jucgarciagon/ELECTROMYOGRAPHIC-SIGNALS/imagen/fortan1.png

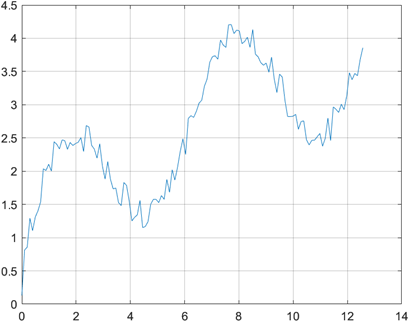
imagen/fortan1.png
