jucgarciagon/ELECTROMYOGRAPHIC-SIGNALS/proyectoV2.1.X/interrupts.c

/******************************************************************************/
/*Files to Include                                                            */
/******************************************************************************/

#if defined(__XC)
    #include <xc.h>         /* XC8 General Include File */
#elif defined(HI_TECH_C)
    #include <htc.h>        /* HiTech General Include File */
#elif defined(__18CXX)
    #include <p18cxxx.h>    /* C18 General Include File */
#endif

#if defined(__XC) || defined(HI_TECH_C)

#include <stdint.h>         /* For uint8_t definition */
#include <stdbool.h>        /* For true/false definition */

#endif

/******************************************************************************/
/* Interrupt Routines                                                         */
/******************************************************************************/

bool conversionADC;
bool entrada=0;

/* High-priority service */

#if defined(__XC) || defined(HI_TECH_C)
void interrupt high_isr(void)
#elif defined (__18CXX)
#pragma code high_isr=0x08
#pragma interrupt high_isr
void high_isr(void)
#else
#error "Invalid compiler selection for implemented ISR routines"
#endif

{

      /* This code stub shows general interrupt handling.  Note that these
      conditional statements are not handled within 3 seperate if blocks.
      Do not use a seperate if block for each interrupt flag to avoid run
      time errors. */

    /*conversion analogo digital*/
     if (PIR1bits.ADIF == 1) {
        conversionADC = 1;
        PIR1bits.ADIF = 0;  

    }
     
     /*timer 0(led de estado)*/
     if (INTCONbits.TMR0IF) //Antes de mandar el pulso
    { 
        LATCbits.LATC0=~PORTCbits.RC0;
        INTCONbits.TMR0IF = 0;
    }
   

}

/* Low-priority interrupt routine */
#if defined(__XC) || defined(HI_TECH_C)
void low_priority interrupt low_isr(void)
#elif defined (__18CXX)
#pragma code low_isr=0x18
#pragma interruptlow low_isr
void low_isr(void)
#else
#error "Invalid compiler selection for implemented ISR routines"
#endif
{

      /* This code stub shows general interrupt handling.  Note that these
      conditional statements are not handled within 3 seperate if blocks.
      Do not use a seperate if block for each interrupt flag to avoid run
      time errors. */

#if 0

      /* TODO Add Low Priority interrupt routine code here. */

      /* Determine which flag generated the interrupt */
      if(<Interrupt Flag 1>)
      {
          <Interrupt Flag 1=0>; /* Clear Interrupt Flag 1 */
      }
      else if (<Interrupt Flag 2>)
      {
          <Interrupt Flag 2=0>; /* Clear Interrupt Flag 2 */
      }
      else
      {
          /* Unhandled interrupts */
      }

#endif

}
